YaTvik/ESPBike/Images/21927.jpg

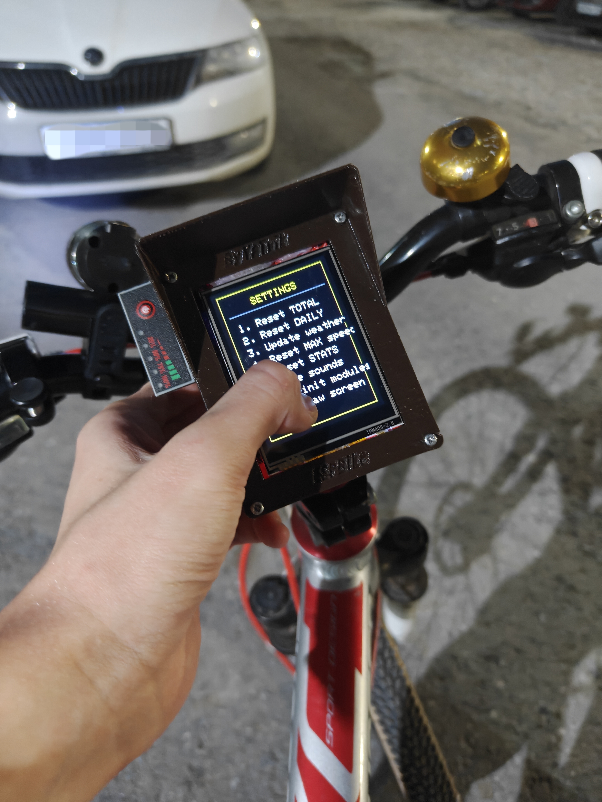
Images/21927.jpg
