YaTvik/ESPBike/Images/21931.jpg

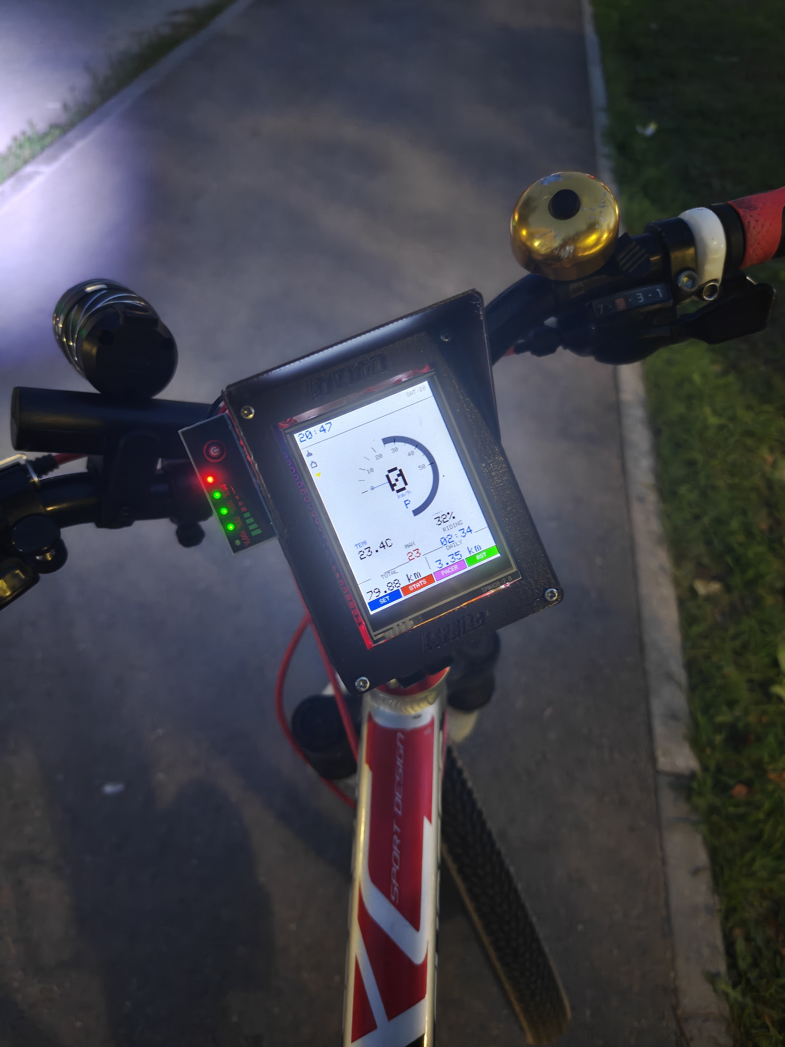
Images/21931.jpg
